sparkfun/RedStick/Documentation/reg_sch/reg.sch

## EAGLE design Documentation/reg_sch/reg.sch (2016-01-29)

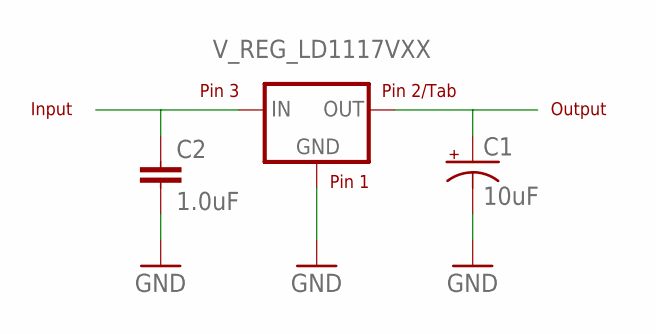
[picture p7: schematic reg.sch]

Parts:
C1: 10uF; EIA3216
C2: 1.0uF; 0603-CAP
U$1: V_REG_LD1117VXX; 78XXL

Connections:
GND: C1.C (-), C2.2, U$1.IN (GND)
unnamed: C2.1, U$1.OUT (IN)
unnamed: C1.A (+), U$1.GND (OUT)

Notes on the sheet:
Pin 1
Pin 2/Tab
Pin 3
Input
Output
